joseph-greiner/tridex_mods/slicer_configuration/bed_textures/bedtexture-tridex-250.png

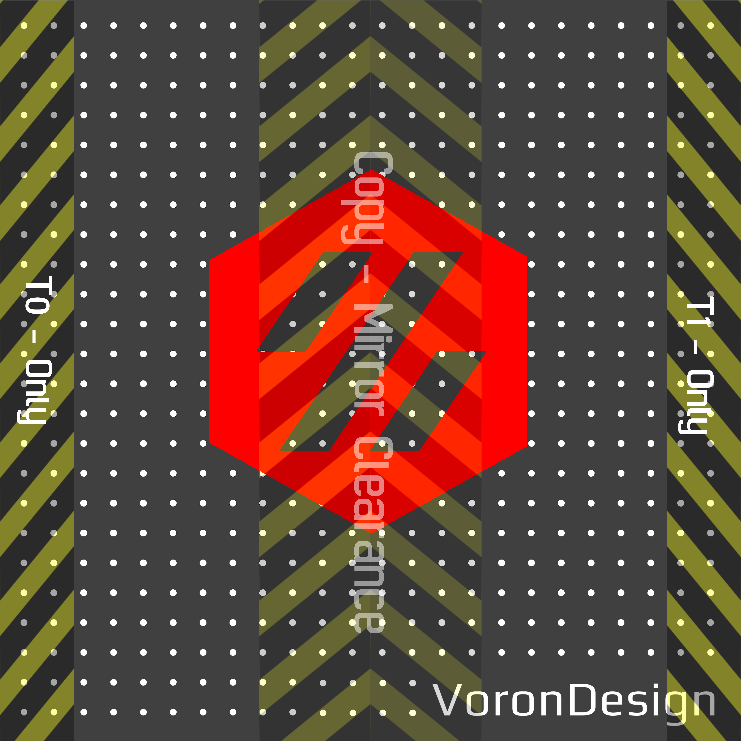
slicer_configuration/bed_textures/bedtexture-tridex-250.png
