joseph-greiner/tridex_mods/slicer_configuration/bed_textures/bedtexture-tridex-300.png

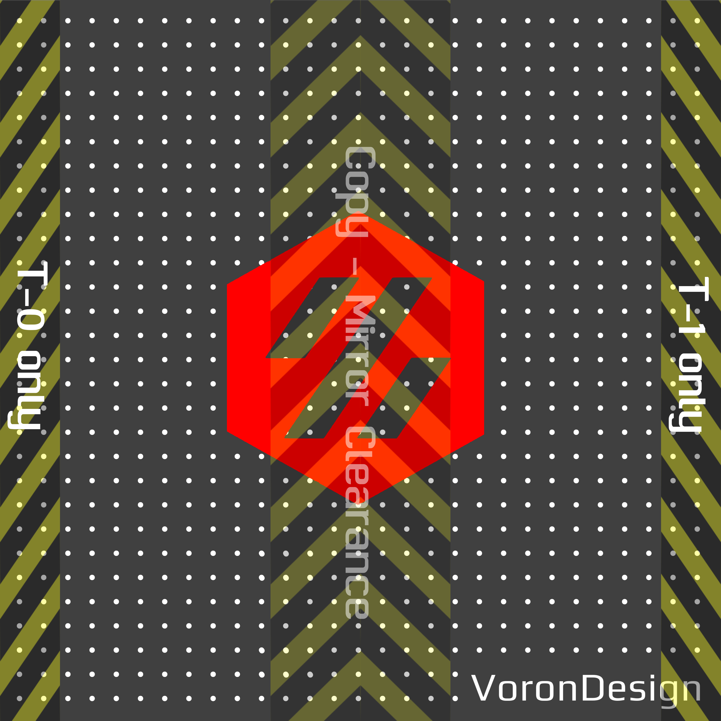
slicer_configuration/bed_textures/bedtexture-tridex-300.png
