joseph-greiner/tridex_mods/front_skirts/STL/revo_nozzle_holder_skirt.stl

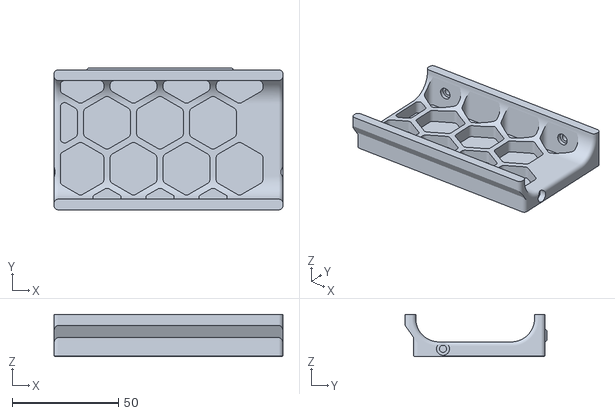
[picture p36: CAD file, 2023-12-05]
front_skirts/STL/revo_nozzle_holder_skirt.stl
108.0 x 66.8 x 20.0
