joseph-greiner/tridex_mods/adjustable_carriage/STL/t1ac_carriage_left.stl

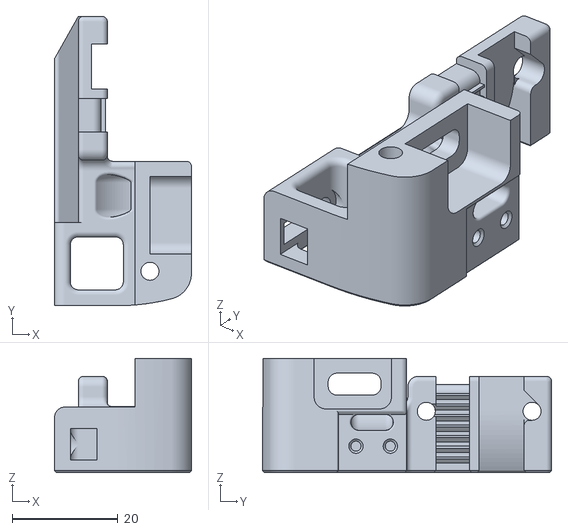
[picture p37: CAD file, 2023-12-05]
adjustable_carriage/STL/t1ac_carriage_left.stl
25.9 x 54.7 x 21.6
