joseph-greiner/tridex_mods/dragon_burner_cowls/STL/t1_cat_cowl_ear_insert.stl

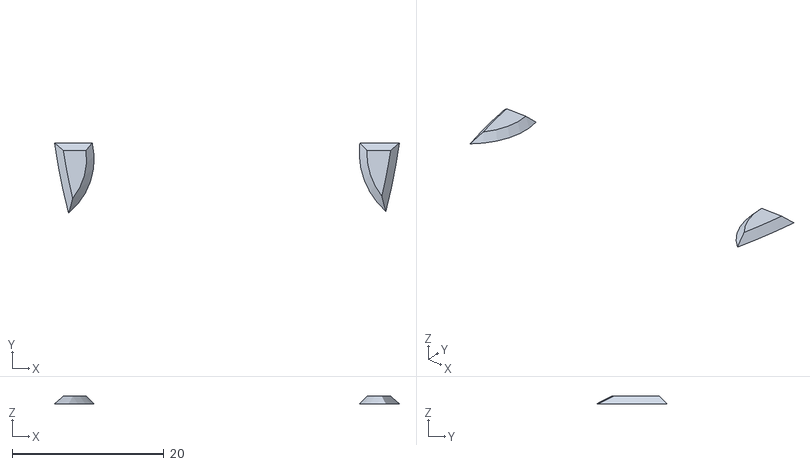
[picture p38: CAD file, 2023-12-05]
dragon_burner_cowls/STL/t1_cat_cowl_ear_insert.stl
45.4 x 9.27 x 1.00
