joseph-greiner/tridex_mods/filament_runout_umbilical_management/STL/bowden_mount_lower_right.stl

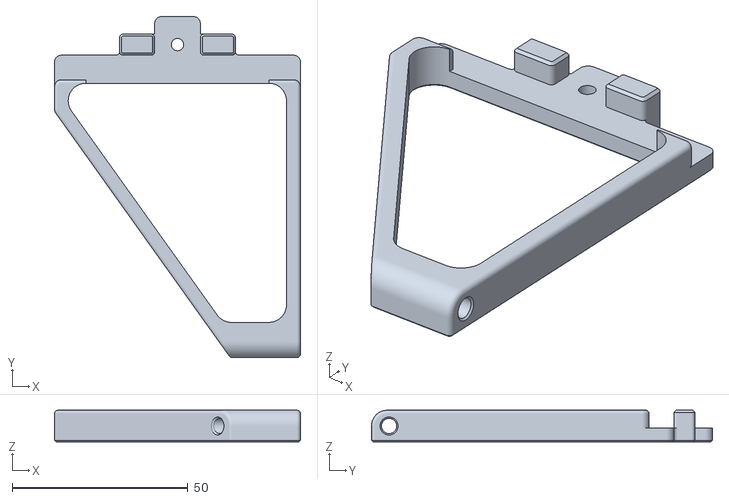
[picture p39: CAD file, 2024-03-18]
filament_runout_umbilical_management/STL/bowden_mount_lower_right.stl
70.0 x 97.0 x 9.00
