joseph-greiner/tridex_mods/front_skirts/STL/revo_nozzle_holder_hinges.stl

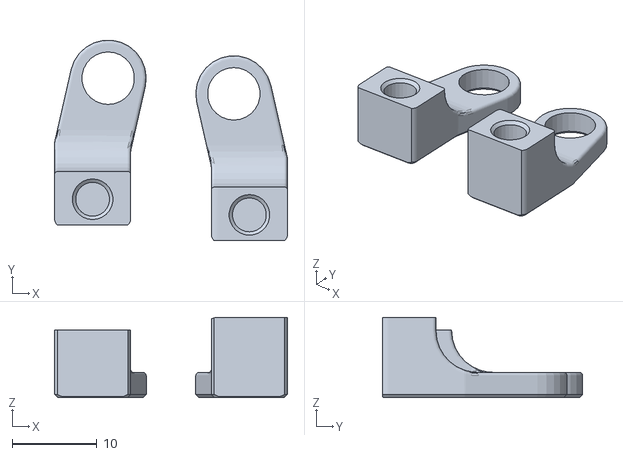
[picture p40: CAD file, 2023-12-05]
front_skirts/STL/revo_nozzle_holder_hinges.stl
27.5 x 23.7 x 9.50
