joseph-greiner/tridex_mods/dragon_burner_cowls/STL/t1_cowl_text.stl

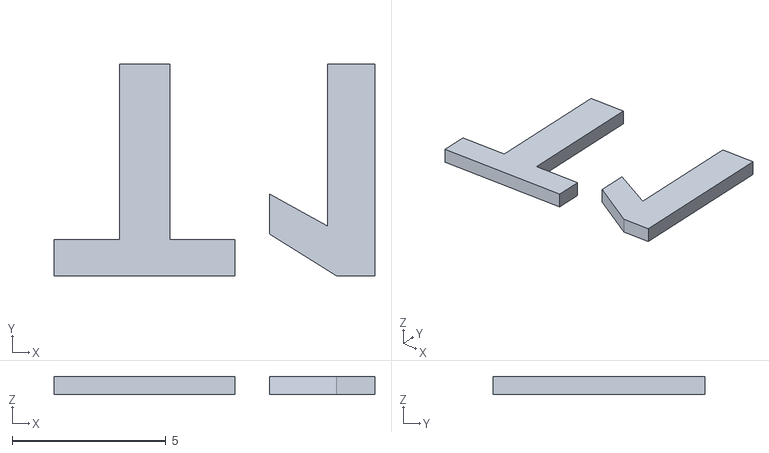
[picture p41: CAD file, 2023-12-05]
dragon_burner_cowls/STL/t1_cowl_text.stl
10.4 x 6.89 x 0.6
