joseph-greiner/tridex_mods/front_skirts/STL/revo_nozzle_holder_door.stl

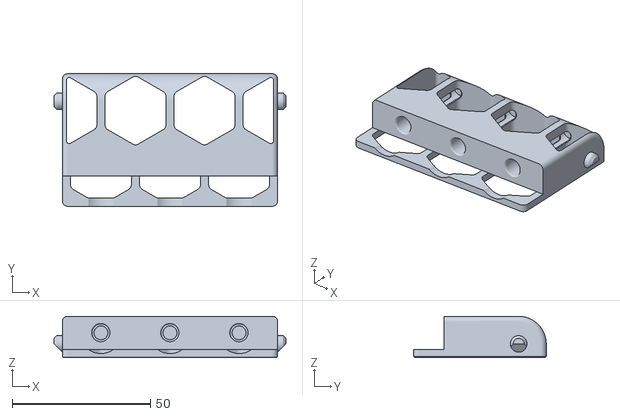
[picture p42: CAD file, 2023-12-05]
front_skirts/STL/revo_nozzle_holder_door.stl
84.0 x 48.0 x 15.0
