joseph-greiner/tridex_mods/filament_runout_umbilical_management/STL/[flex]_bowden_clip_bushing_x3.stl

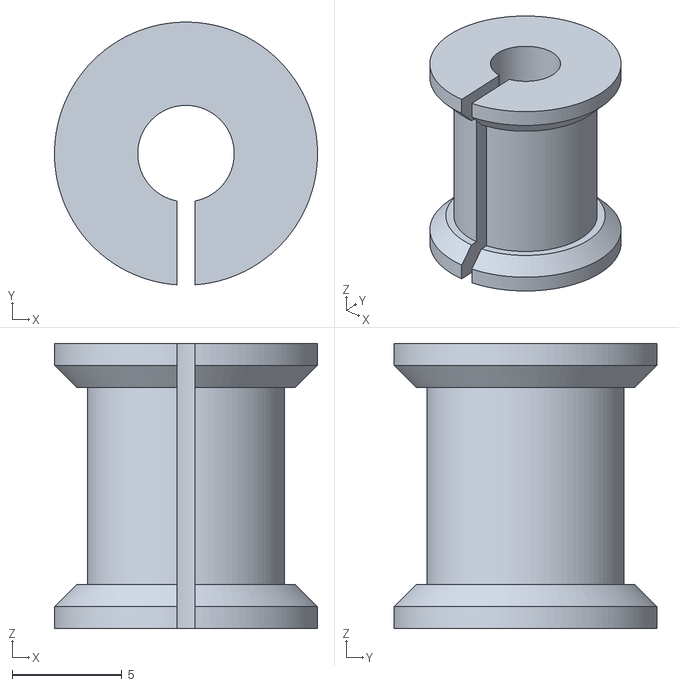
[picture p43: CAD file, 2024-03-18]
filament_runout_umbilical_management/STL/[flex]_bowden_clip_bushing_x3.stl
12.0 x 12.0 x 13.0
