joseph-greiner/tridex_mods/adjustable_carriage/STL/ac_tool_mount_right.stl

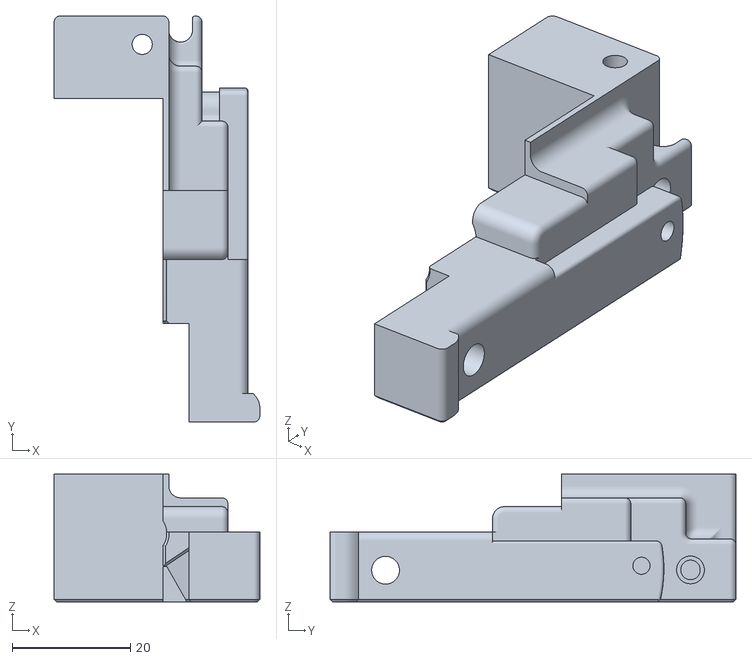
[picture p44: CAD file, 2023-12-05]
adjustable_carriage/STL/ac_tool_mount_right.stl
34.8 x 68.7 x 21.6
