joseph-greiner/tridex_mods/dragon_burner_cowls/STL/t0_cowl_text.stl

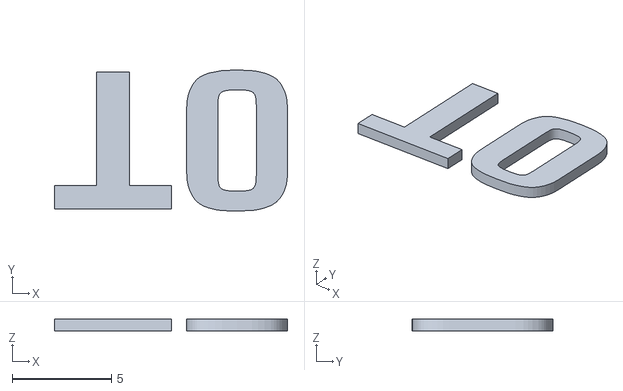
[picture p45: CAD file, 2023-12-05]
dragon_burner_cowls/STL/t0_cowl_text.stl
11.7 x 7.10 x 0.6
