joseph-greiner/tridex_mods/dragon_burner_cowls/STL/t1_cat_cowl.stl

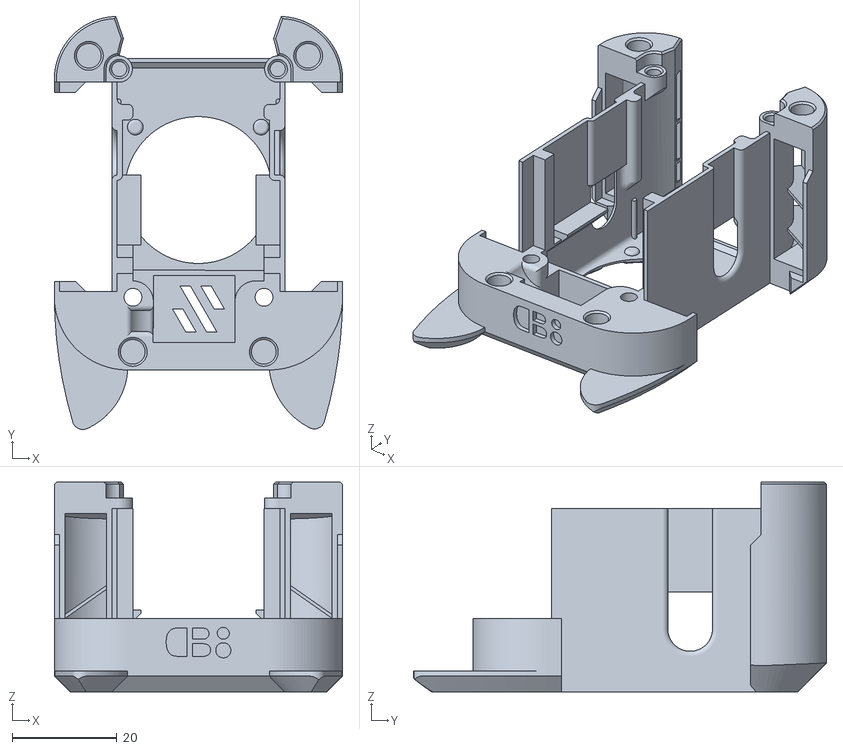
[picture p46: CAD file, 2023-12-05]
dragon_burner_cowls/STL/t1_cat_cowl.stl
55.0 x 78.8 x 40.0
