joseph-greiner/tridex_mods/printer_configuration/toolboard_0.cfg

# This file contains common pin mappings for the BigTreeTech EBB36 V1.2
# when setup for T0 on Tridex
#####################################################################
#   Extruder
#####################################################################

[extruder]
step_pin: toolboard_0: PD0
dir_pin: toolboard_0: PD1
enable_pin: !toolboard_0: PD2
##  Update value below when you perform extruder calibration
##  If you ask for 100mm of filament, but in reality it is 98mm:
##  rotation_distance = <previous_rotation_distance> * <actual_extrude_distance> / 100
##  22.678 is a good starting point for CW2
##--------------------------------------------------------------------
rotation_distance: 22.678
##--------------------------------------------------------------------
gear_ratio: 50:10 # CW2 gear ratio

microsteps: 32
full_steps_per_rotation: 200
nozzle_diameter: 0.40
filament_diameter: 1.75

max_extrude_cross_section: 1.75
max_extrude_only_distance: 100.0

#####################################################################
#   Heater
#####################################################################

heater_pin: toolboard_0: PB13
sensor_type: ATC Semitec 104NT-4-R025H42G
sensor_pin: toolboard_0: PA3
min_temp: 0
max_temp: 270
max_power: 1.0

min_extrude_temp: 170

##--------------------------------------------------------------------
## Pressure Advance
#pressure_advance: 0.040             # Try to keep pressure_advance below 1.0
#pressure_advance_smooth_time: 0.040 # Default is 0.040, leave stock
##--------------------------------------------------------------------

##  Make sure to update below for your relevant driver (2208 or 2209)
[tmc2209 extruder]
uart_pin: toolboard_0: PA15
interpolate: false
run_current: 0.50
sense_resistor: 0.110
stealthchop_threshold: 0

#####################################################################
#   Fan Control
#####################################################################

[fan_generic print_cooling_t0]
##  Print Cooling Fan
pin: toolboard_0: PA0
kick_start_time: 0.5
off_below: 0.10

## Hotend fan
[heater_fan extruder_fan]
Pin: toolboard_0: PA1
max_power: 1.0
kick_start_time: 0.5
heater: extruder
heater_temp: 50.0
##  If you are experiencing back flow, you can reduce fan_speed
fan_speed: 1.0

#####################################################################
#   Accelerometer
#####################################################################

[adxl345 toolboard_0]
cs_pin: toolboard_0: PB12
spi_software_sclk_pin: toolboard_0: PB10
spi_software_mosi_pin: toolboard_0: PB11
spi_software_miso_pin: toolboard_0: PB2
axes_map: z,y,x

[resonance_tester]
accel_chip: adxl345 toolboard_0
probe_points:
    150, 150, 50
